gluonsandquarks/tiny-osean/rev b/70mm-osean/.svg2shenzhen-cache/images/B.Mask_g29.png

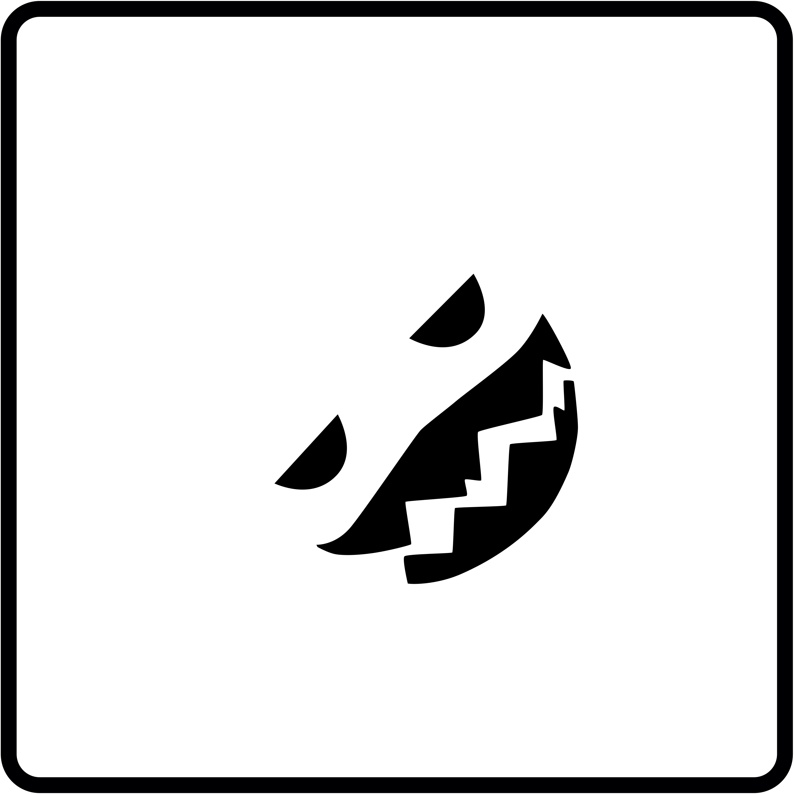
rev b/70mm-osean/.svg2shenzhen-cache/images/B.Mask_g29.png
