gluonsandquarks/tiny-osean/rev b/70mm-osean/.svg2shenzhen-cache/images/B.SilkS_g31.png

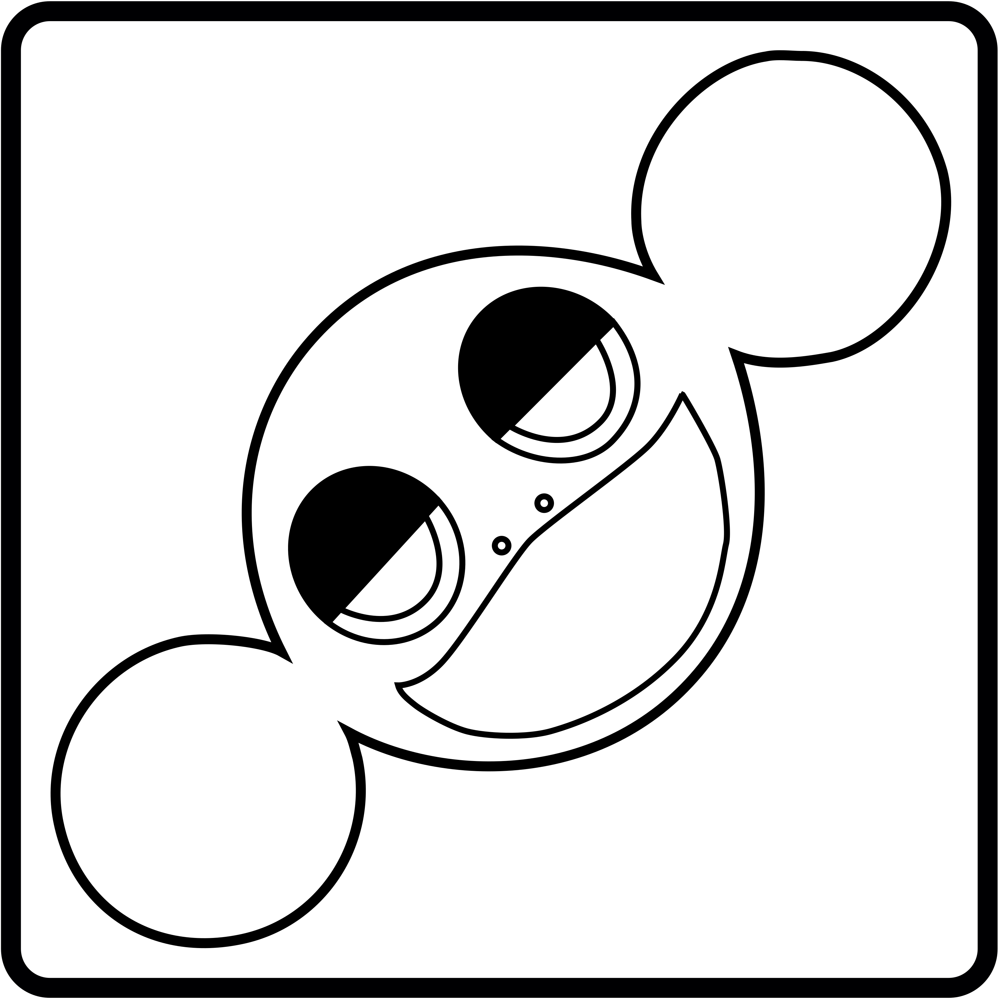
rev b/70mm-osean/.svg2shenzhen-cache/images/B.SilkS_g31.png
