gluonsandquarks/tiny-osean/rev b/70mm-osean/.svg2shenzhen-cache/images/F.Mask_g23.png

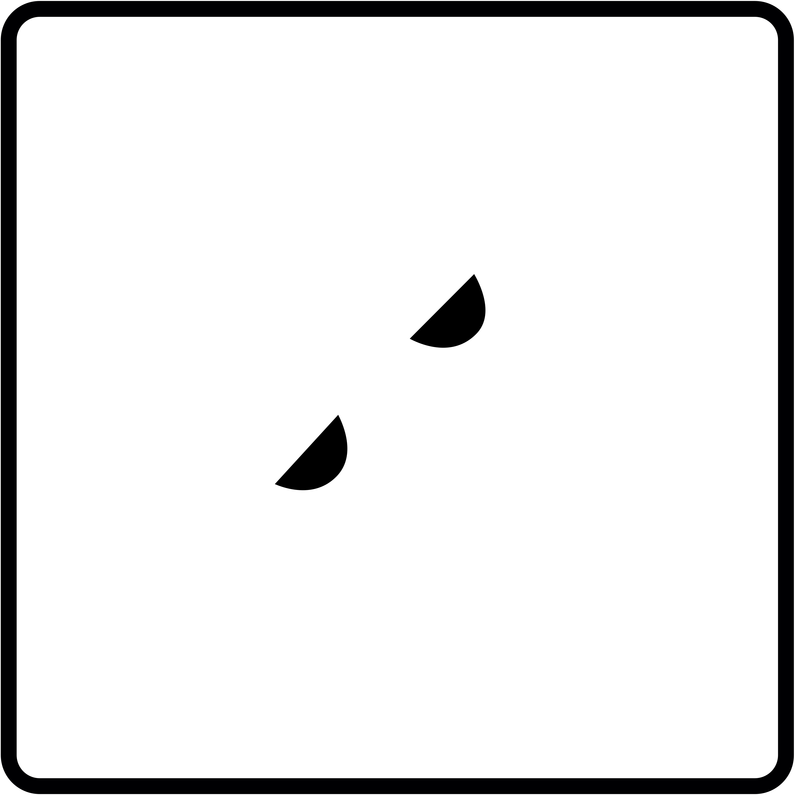
rev b/70mm-osean/.svg2shenzhen-cache/images/F.Mask_g23.png
