gluonsandquarks/tiny-osean/rev b/70mm-osean/.svg2shenzhen-cache/images/F.SilkS_g25.png

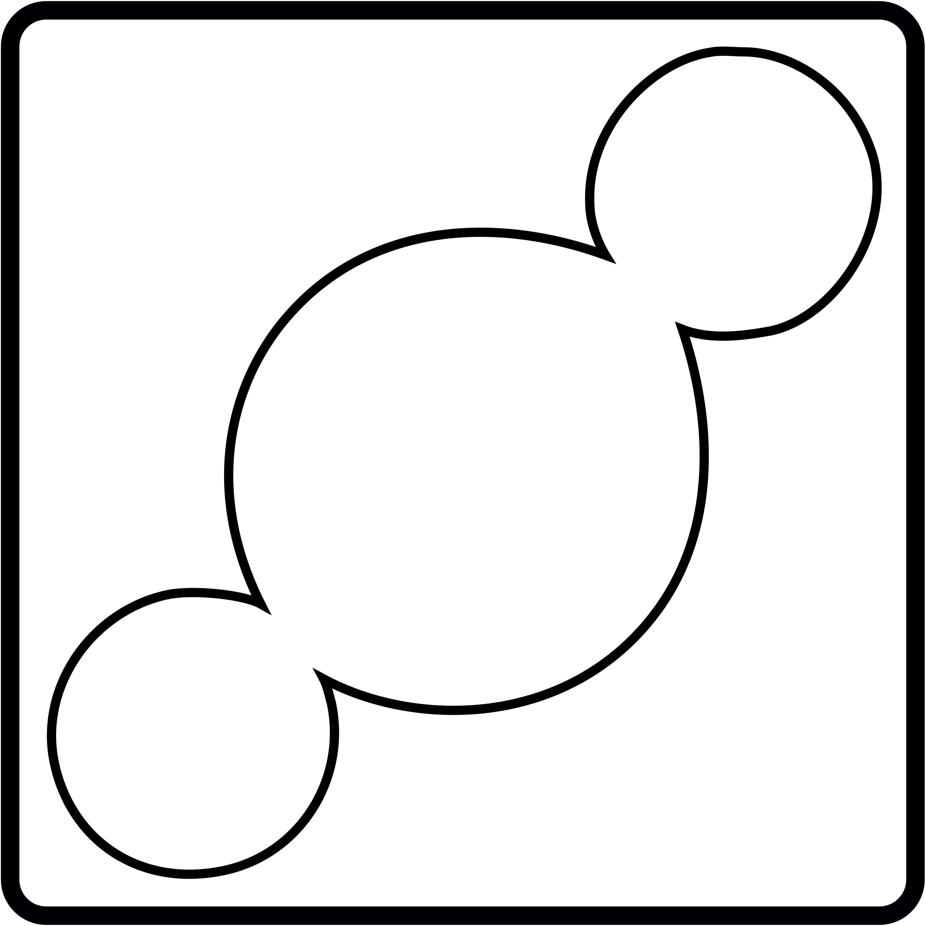
rev b/70mm-osean/.svg2shenzhen-cache/images/F.SilkS_g25.png
